petervflocke/Pico-CatanDice/docs/IMG20230221010017.jpg

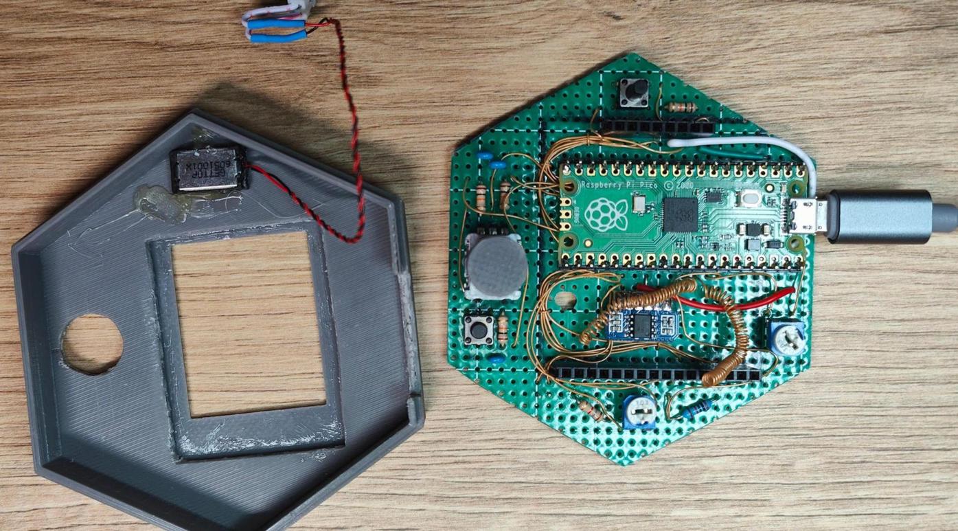
docs/IMG20230221010017.jpg
