petervflocke/Pico-CatanDice/docs/IMG20230221221409.jpg

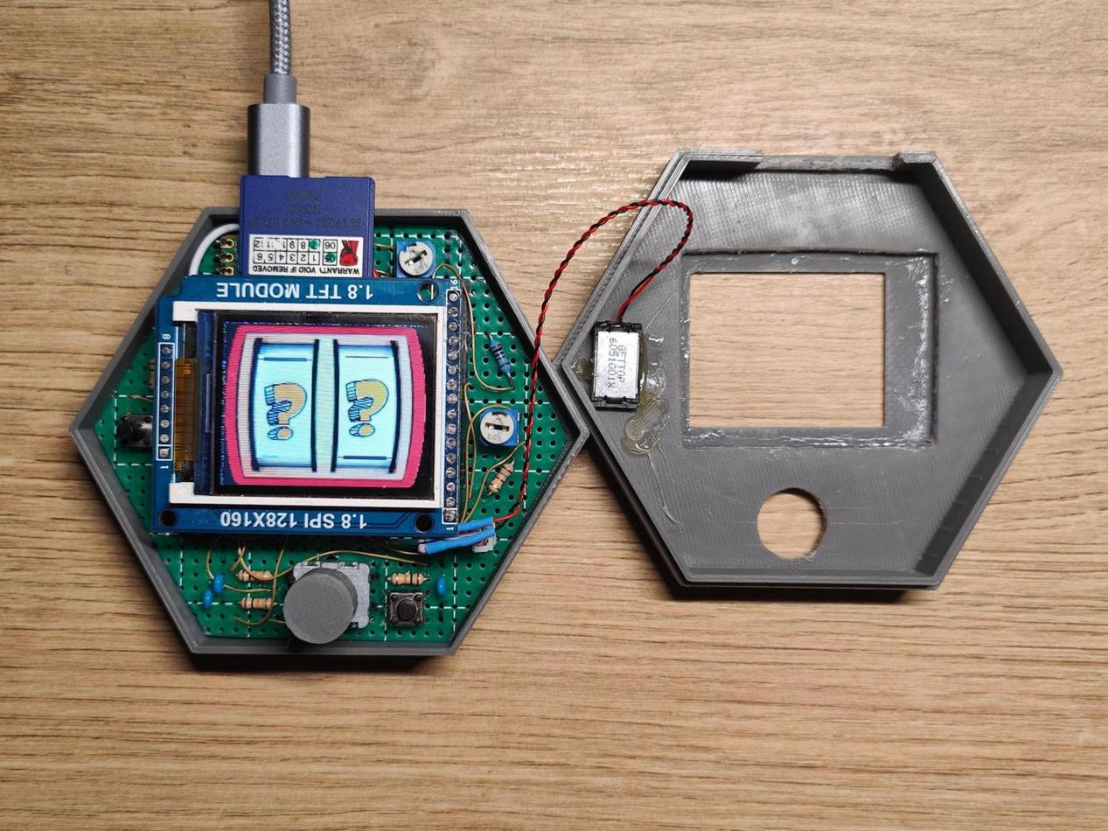
docs/IMG20230221221409.jpg
