petervflocke/Pico-CatanDice/docs/IMG20230221221504.jpg

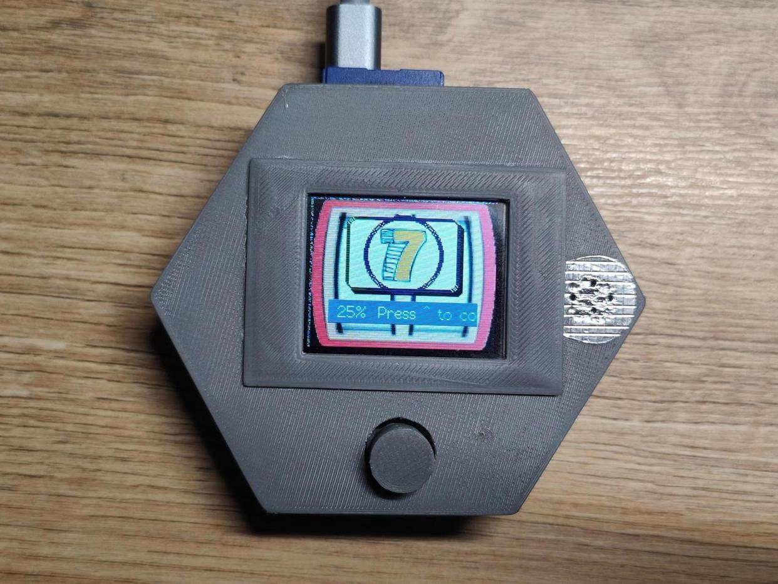
docs/IMG20230221221504.jpg
