petervflocke/Pico-CatanDice/docs/IMG20230221221529.jpg

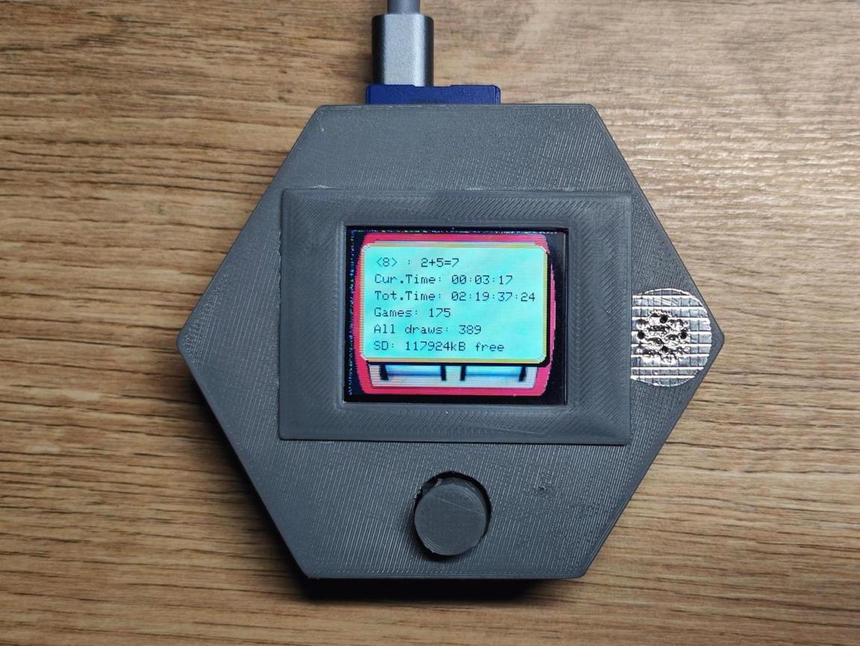
docs/IMG20230221221529.jpg
