petervflocke/Pico-CatanDice/docs/IMG20230221221900.jpg

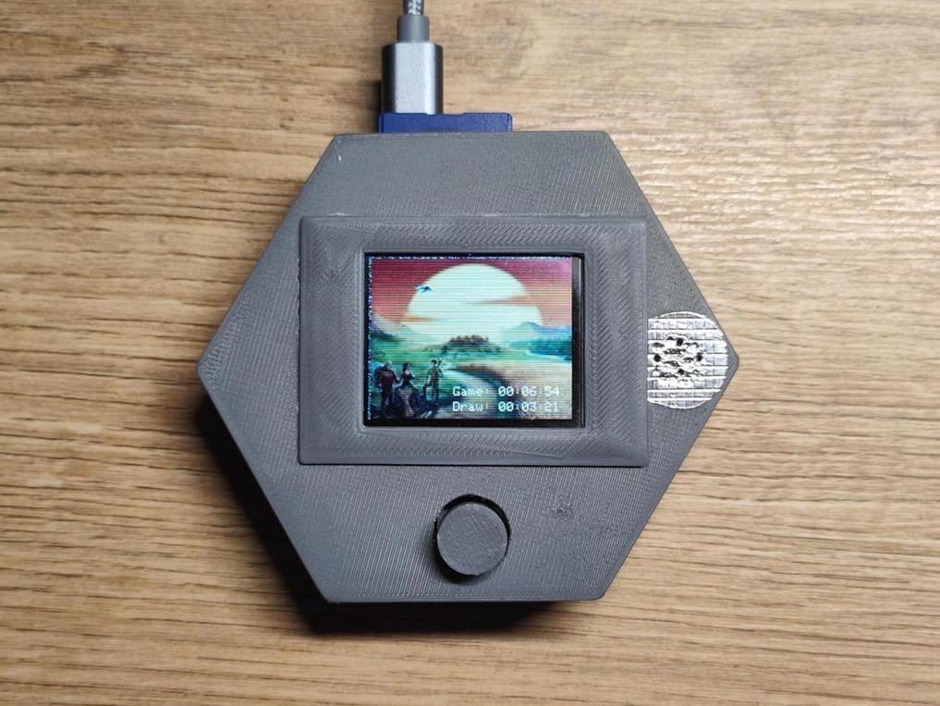
docs/IMG20230221221900.jpg
