petervflocke/Pico-CatanDice/docs/IMG20230221222317.jpg

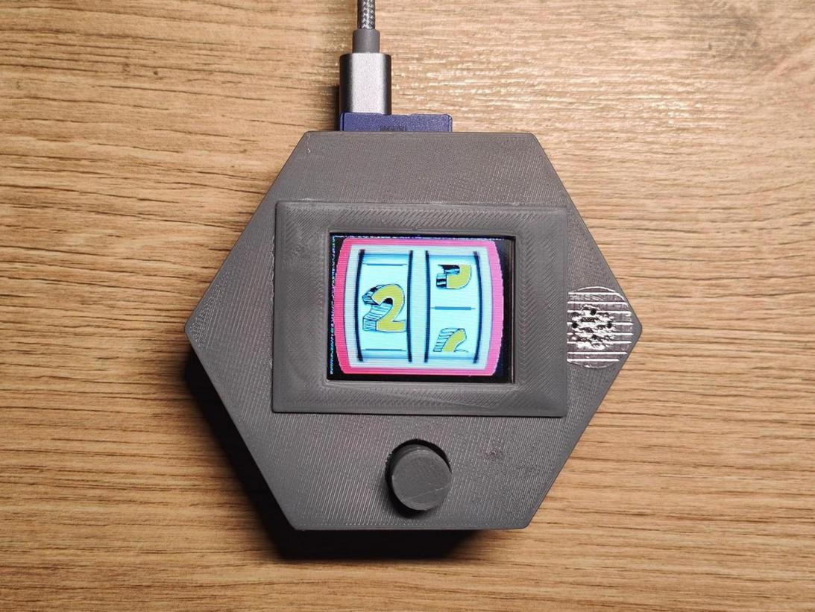
docs/IMG20230221222317.jpg
