petervflocke/Pico-CatanDice/docs/IMG20230222221912.jpg

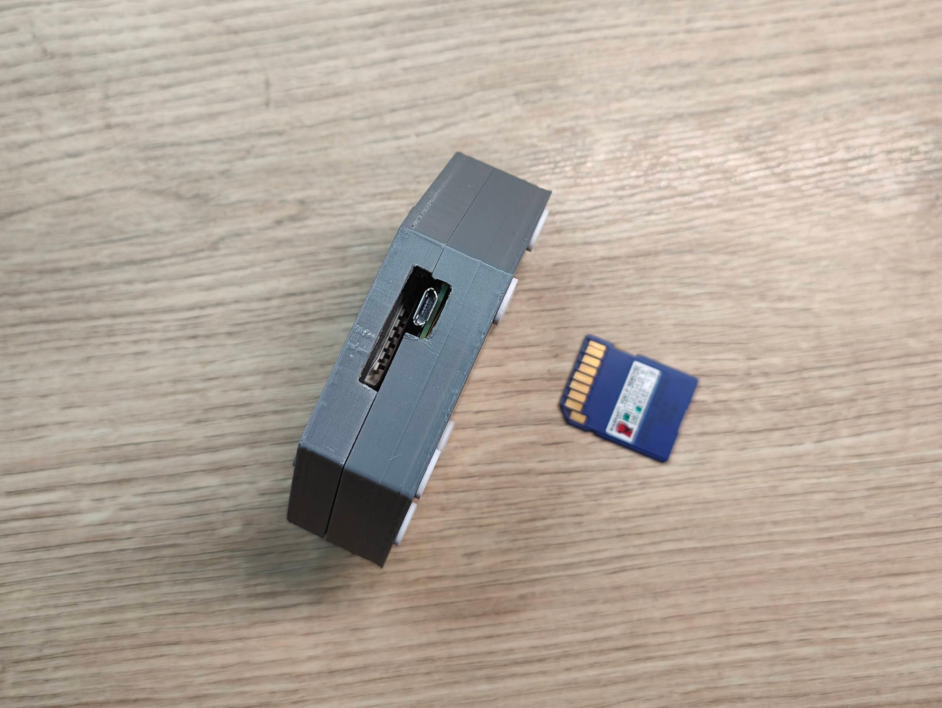
docs/IMG20230222221912.jpg
