petervflocke/Pico-CatanDice/src/counter.h

/* cSpell:disable */
#pragma once
#ifndef COUNTER_H
#define COUNTER_H_

#include "Arduino.h"

const uint16_t counterWidth  = 158;
const uint16_t counterHeight = 126;

const unsigned short counter[] PROGMEM ={
0x1081, 0x1081, 0x1081, 0x1081, 0x1081, 0x1081, 0x1081, 0x1081, 0x1081, 0x18c1, 0x61a5, 0xc3ab, 0xba48, 0xc228, 0xdb0a, 0xdb0a, 0xdb0a, 0xdb0a, 0xdb0a, 0xdb0a, 0xdb0a, 0xdb0a, 0xdb0a, 0xdb0a, 0xdb0a, 0xca89, 0xca89, 0xcae9, 0xcae9, 0xcae9, 0xcae9, 0xcae9, 0xca89, 0xcae9, 0xca89, 0xca89, 0xca89, 0xca89, 0xca89, 0xca89, 0xca89, 0xca89, 0xca89, 0xca89, 0xba48, 0xba48, 0xba48, 0xba48, 0xba48, 0xba48, 0xba48, 0xba48, 0xba48, 0xb1e7, 0xb1e7, 0xb1e7, 0xb1e7, 0xb1e7, 0xb1e7, 0xb1e7, 0xb1e7, 0xb1e7, 0xb1e7, 0xb1e7, 0xb1e7, 0xb1e7, 0xb1e7, 0xb1e7, 0xb1e7, 0xb1e7, 0xb1e7, 0xb1e7, 0xb1e7, 0xb1e7, 0xb1e7, 0xb1e7, 0xb1e7, 0xb1e7, 0xb1e7, 0xb1e7, 0xb1e7, 0xb1e7, 0xb1e7, 0xb1e7, 0xb1e7, 0xb1e7, 0xb1e7, 0xb1e7, 0xb1e7, 0xb1e7, 0xb1e7, 0xb1e7, 0xb1e7, 0xb1e7, 0xb1e7, 0xb1e7, 0xb1e7, 0xb1e7, 0xb1e7, 0xb1e7, 0xb1e7, 0xb1e7, 0xb1e7, 0xb1e7, 0xb1e7, 0xba48, 0xba48, 0xba48, 0xba48, 0xba48, 0xba48, 0xba48, 0xba48, 0xba48, 0xca89, 0xca89, 0xca89, 0xca89, 0xca89, 0xca89, 0xca89, 0xca89, 0xca89, 0xca89, 0xca89, 0xca89, 0xca89, 0xca89, 0xca89, 0xca89, 0xca89, 0xca89, 0xca89, 0xca89, 0xca89, 0xdb0a, 0xdb0a, 0xdb0a, 0xdb0a, 0xdb0a, 0xca89, 0xca89, 0xba48, 0xb1e7, 0xb1e7, 0xc309, 0x7a06, 0x4964, 0x18c1, 0x1081, 0x1081, 0x1081, 0x1081, 0x1081, 0x1081, 0x1081, 0x1081, 0x1081, 
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
};
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
