petervflocke/Pico-CatanDice/src/graphics.h

/* cSpell:disable */
#pragma once
#ifndef GRAPHICS_H
#define GRAPHICS_H

#include "Arduino.h"
#include "SdFat.h"
#include "picData.h"
// #include "reelpic.h"

// define posistion of the graphic elements
// position of the left and right reel of digits
#define lx 26
#define ly 24
#define rx 90
#define ry 24


// Position of status LED on screen
#define ledSize  16
#define ledPosX 135
#define ledPosY   0

// Result windows position
#define rRX  30 /* result box upper x*/
#define rRY  15 /* result box uper y*/
#define rWi  96 /* result box width */
#define rHi  62 /* result box high */
#define mHi  47 /* minimal digit size */
#define dSt  18 /* digit start line*/
#define rBl 128 /* scroll bar lenghth*/
#define rBh  20 /* scroll bar high */

// Display statistics
#define sRX   7 /* stat box upper x*/
#define sRY  20 /* stat box uper y*/
#define sWi 143 /* stat box width */
#define sHi  80 /* stat box high */
#define sXY  10 /* margin of 0,0 from boarders*/
#define sBw   5 /* bar width */
#define sBm   5 /* gap between bars */


/* Useful Macros for getting elapsed time */
#define SECS_PER_MIN  (60UL)
#define SECS_PER_HOUR (3600UL)
#define SECS_PER_DAY  (SECS_PER_HOUR * 24L)
#define numberOfSeconds(_time_) (_time_ % SECS_PER_MIN)  
#define numberOfMinutes(_time_) ((_time_ / SECS_PER_MIN) % SECS_PER_MIN) 
#define numberOfHours(_time_) (( _time_% SECS_PER_DAY) / SECS_PER_HOUR)
#define elapsedDays(_time_) ( _time_ / SECS_PER_DAY)  


typedef enum {
  left_and_Right,  
  sum_of_both
} BarChartType;

struct birdStruc
  {
    const unsigned int bx;
    const unsigned int by;
    const unsigned int b_width;
    const unsigned int b_height;
    const unsigned short *bird;
  };

extern birdStruc tabBirds[];

extern const unsigned short *space;
extern const unsigned short *qq;
extern const unsigned short *digits[];
extern const unsigned short *ptr;
extern const unsigned short *ptr_start;
extern const unsigned short *ptr_stop;
extern const unsigned int top_pos;

const char MessageText1[] PROGMEM = "Press to continue. [%d] L: %d %.0f%%  |  R: %d %.0f%%  |  S: %d  %.0f%%";
const char InfoText1[] PROGMEM = "<%lu> : %d+%d=%d";
const char InfoText2[] PROGMEM = "Cur.Time: %02u:%02u:%02u";
const char InfoText3[] PROGMEM = "Tot.Time: %02u:%02u:%02u:%02u";
const char InfoText4[] PROGMEM = "Games:%lu, draws:%lu";
const char InfoText5[] PROGMEM = "Battery: %4.2fV";
const char InfoText6[] PROGMEM = "SD Card Error";
const char InfoText7[] PROGMEM = "Line error: %lu";
const char InfoText8[] PROGMEM = "SD: %lukB free";

const char  InfoText9[] PROGMEM = "Game: %02u:%02u:%02u";
const char InfoText10[] PROGMEM = "Draw: %02u:%02u:%02u";
const char InfoText11[] PROGMEM = "%2d"; // backlight
const char InfoText12[] PROGMEM = "Backlight"; 
const char InfoText13[] PROGMEM = "%3.0f%%"; 


#define MessageLen 128 /*length of message*/

void drawInfoBox(TFT_eSPI &tft);
void drawBarChart(TFT_eSPI &tft, u_int32_t statTabL[], u_int32_t statTabR[], u_int32_t statTabS[], u_int32_t statCnt, BarChartType statTab, char* titel);
void drawChart(TFT_eSPI &tft, u_int32_t* statTabX, int maxIndex, int deltaIndex);
void showSDError(TFT_eSPI &tft);
void drawInfoText(TFT_eSPI &tft, int rndl, int rndr, unsigned long cnt, SdFat32 &myCard, double BatVol);
void restoreBack(TFT_eSPI &tft, unsigned int posX, unsigned int posY, unsigned int b_width, unsigned int b_hight, unsigned int s_width, const unsigned short *sourceBuf);
// void nextBird(TFT_eSPI &tft, unsigned int, unsigned int, unsigned int);
void drawTime(TFT_eSPI &tft, unsigned int ttX, unsigned int ttY, unsigned long ttd);
void drawBacklight(TFT_eSPI &tft, int, boolean);
void drawBatVol(TFT_eSPI &tft, double batVol);

#endif
